bajraan/Sienkiewicz_TOUCH/__QR/Github.Sienkiewicz_TOUCH.png

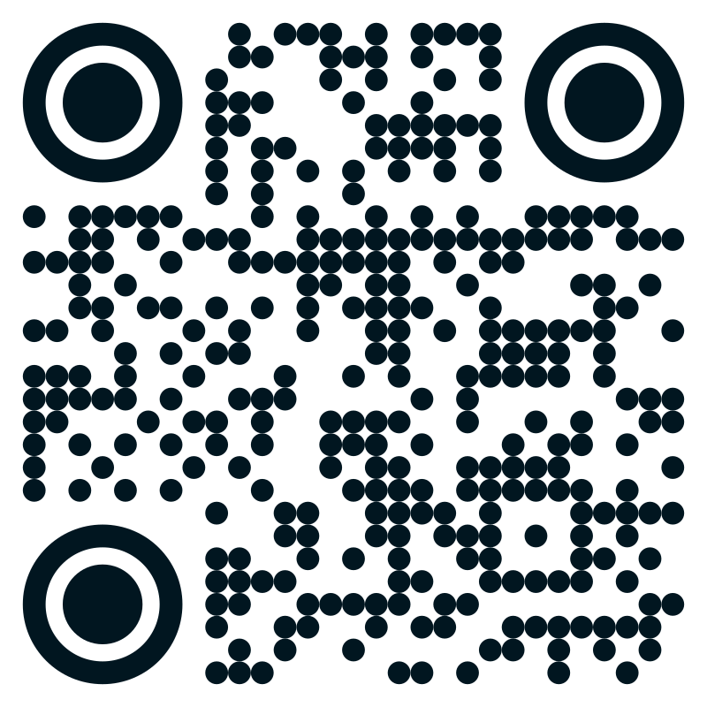
__QR/Github.Sienkiewicz_TOUCH.png
