bajraan/Sienkiewicz_TOUCH/HTML/images/cat_pdf_drill_map_Sienkiewicz_TOUCH-PTH_drill_map.png

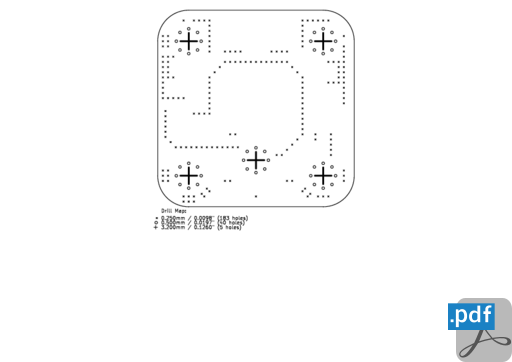
HTML/images/cat_pdf_drill_map_Sienkiewicz_TOUCH-PTH_drill_map.png
