bajraan/Sienkiewicz_TOUCH/HTML/images/cat_png_3d_viewer_angled_bottom_Sienkiewicz_TOUCH-angled_bottom.png

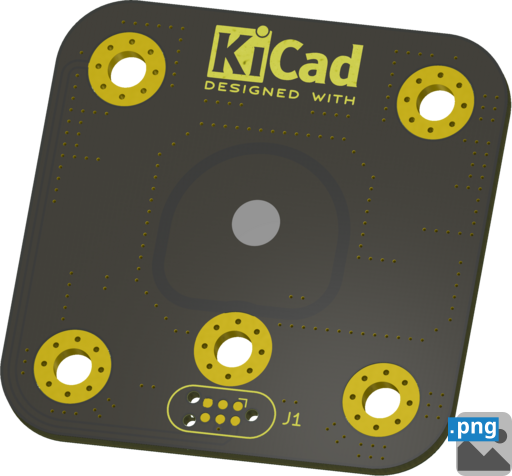
HTML/images/cat_png_3d_viewer_angled_bottom_Sienkiewicz_TOUCH-angled_bottom.png
