bajraan/Sienkiewicz_TOUCH/HTML/images/cat_png_3d_viewer_bottom_Sienkiewicz_TOUCH-bottom.png

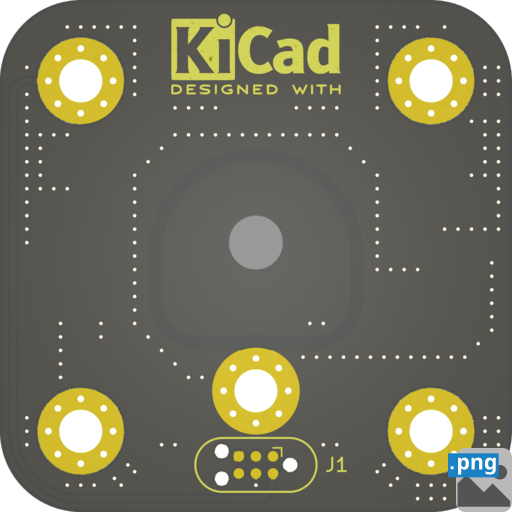
HTML/images/cat_png_3d_viewer_bottom_Sienkiewicz_TOUCH-bottom.png
