bajraan/Sienkiewicz_TOUCH/HTML/images/cat_png_3d_viewer_top_Sienkiewicz_TOUCH-top.png

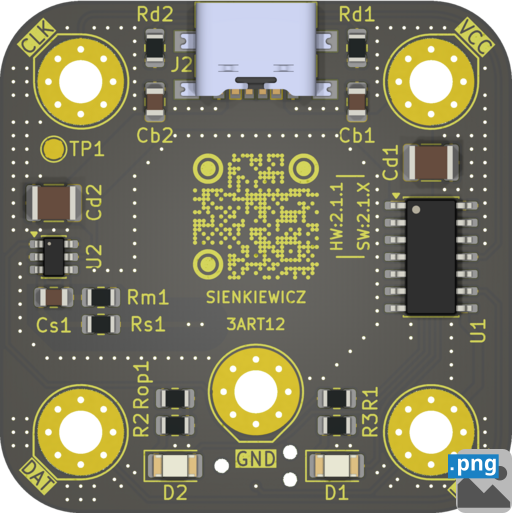
HTML/images/cat_png_3d_viewer_top_Sienkiewicz_TOUCH-top.png
