bajraan/Sienkiewicz_TOUCH/Manufacturing/Fabrication/Sienkiewicz_TOUCH-fabrication.pdf

# Top Fabrication (Scale 1:1)

# 3ART12 TOUCH Fabrication Document

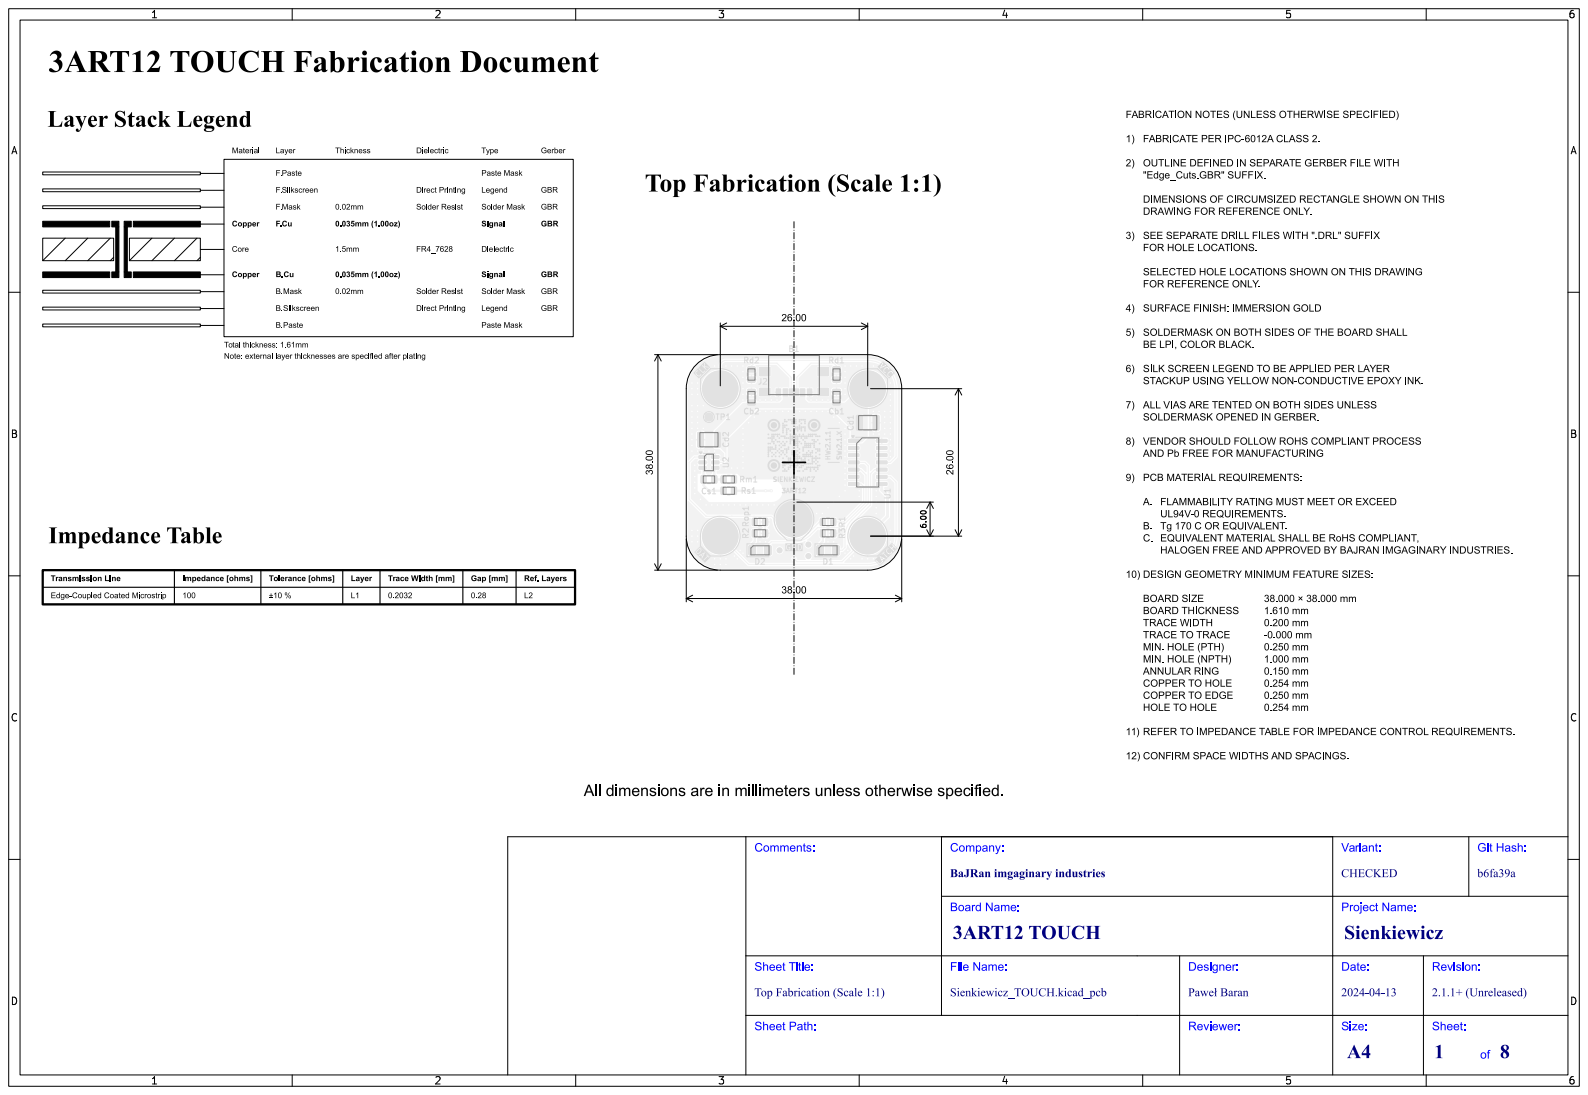
[picture p15: page 1]

# Bottom Fabrication (Scale 1:1)

# 3ART12 TOUCH Fabrication Document

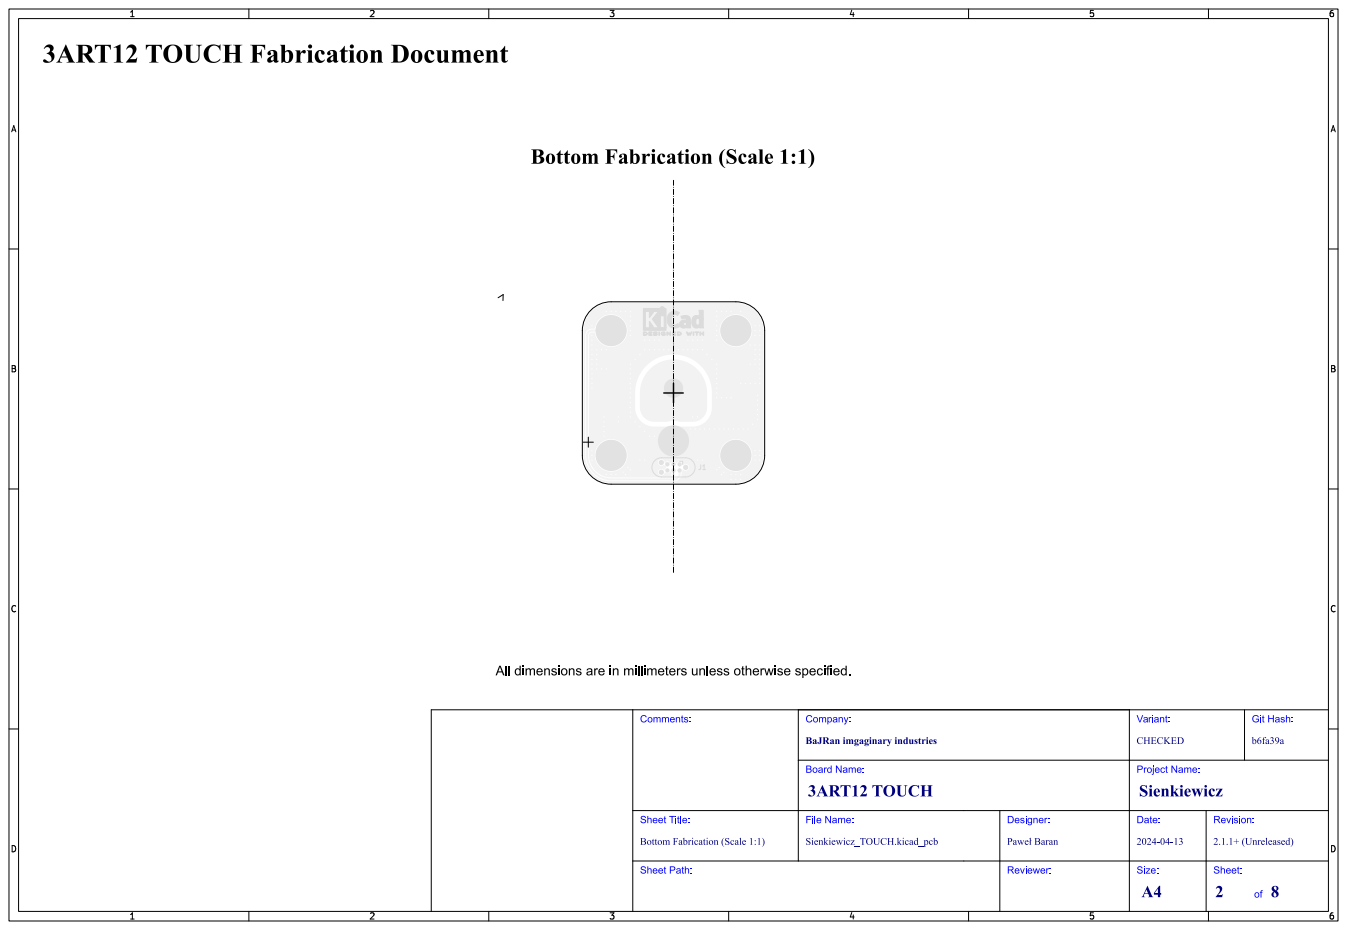
[picture p16: page 2]
Git; Hash:; Comments:; Sheet Path:; Sheet Title:; File Name:; 3ART12 TOUCH; Sienkiewicz; Company:; CHECKED; Variant:; Board Name:; Sienkiewicz_TOUCH.kicad_pcb; Paweł Baran; Designer:; Reviewer:; Project Name:; Date:; 2.1.1+ (Unreleased); Revision:; Size:; Sheet:

BaJRan imgaginary industries

Bottom Fabrication (Scale 1:1)

# Drill Drawing L1 - L2 (Scale 1:1)

# 3ART12 TOUCH Fabrication Document

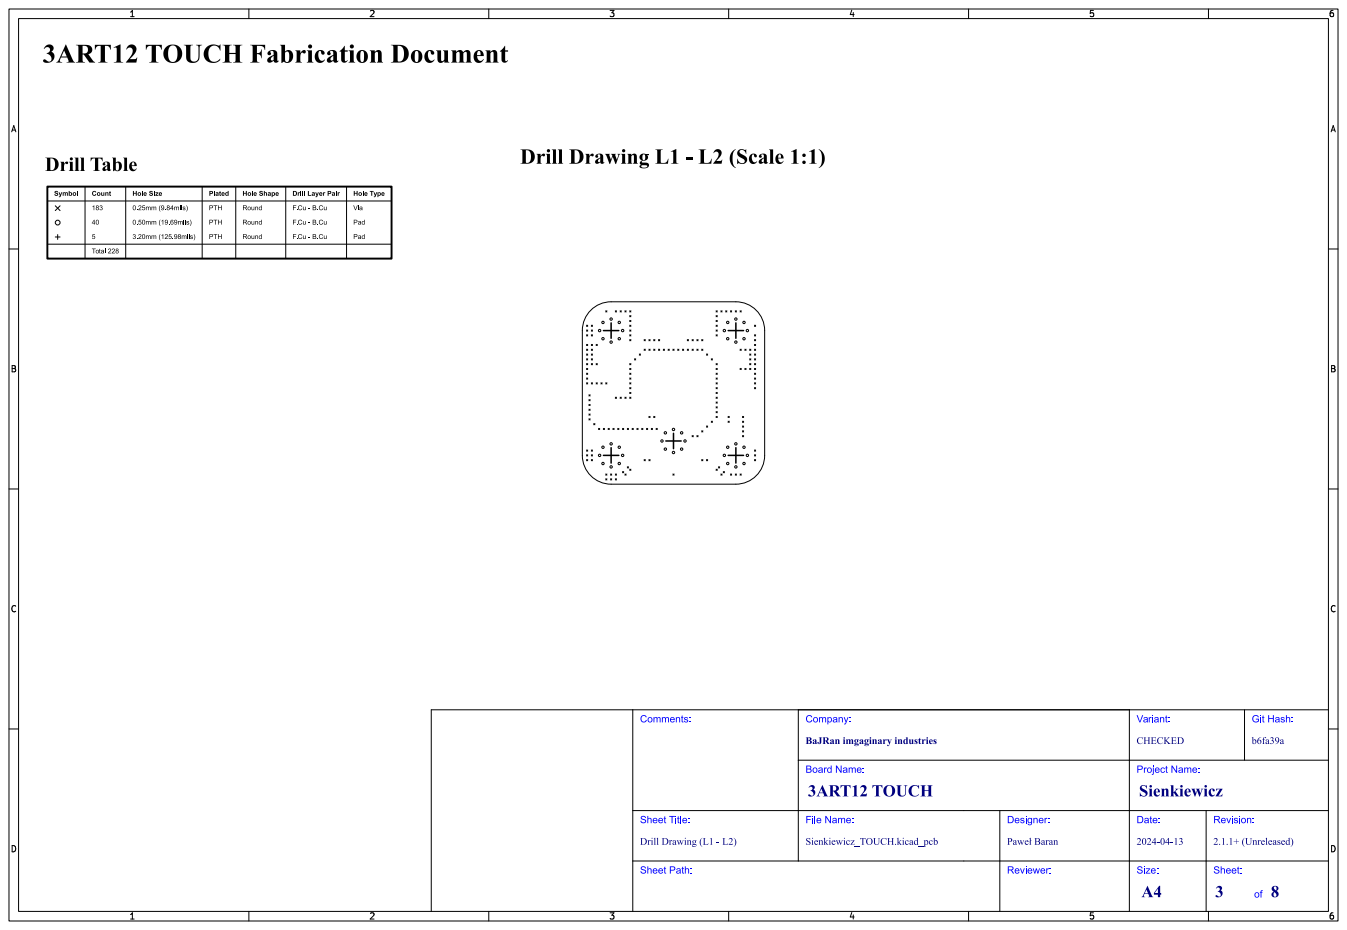
[picture p17: page 3]
Git; Hash:; Comments:; Drill Drawing (L1 - L2); Sheet Path:; Sheet Title:; File Name:; 3ART12 TOUCH; Sienkiewicz; Company:; CHECKED; Variant:; Board Name:; Sienkiewicz_TOUCH.kicad_pcb; Paweł Baran; Designer:; Reviewer:; Project Name:; Date:; 2.1.1+ (Unreleased); Revision:; Size:; Sheet:

BaJRan imgaginary industries

# Drill Drawing L1 - L2 (Scale 1:1)

# 3ART12 TOUCH Fabrication Document

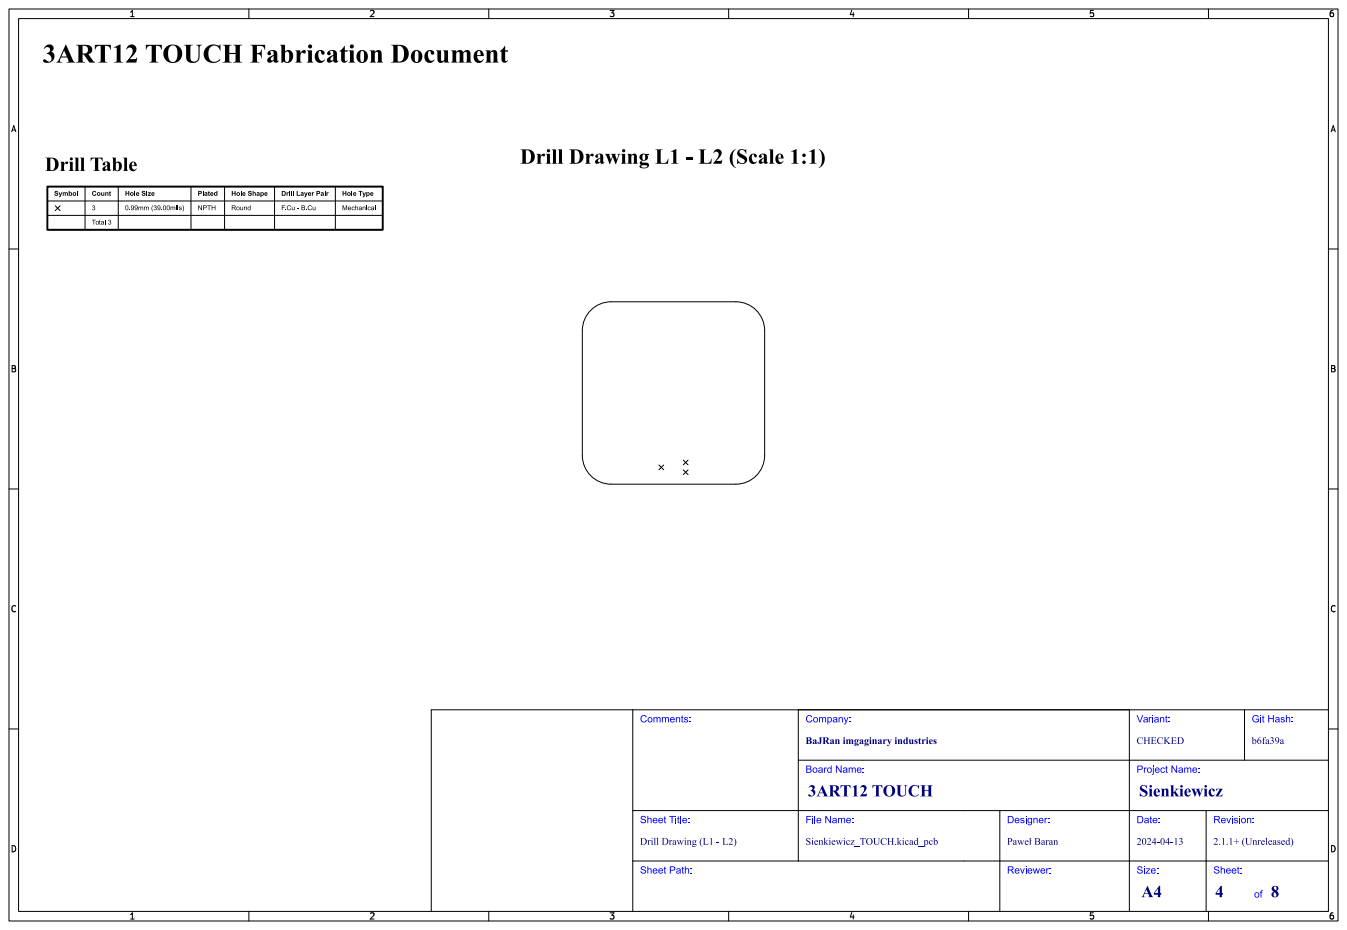
[picture p18: page 4]
Git; Hash:; Comments:; Drill Drawing (L1 - L2); Sheet Path:; Sheet Title:; File Name:; 3ART12 TOUCH; Sienkiewicz; Company:; CHECKED; Variant:; Board Name:; Sienkiewicz_TOUCH.kicad_pcb; Paweł Baran; Designer:; Reviewer:; Project Name:; Date:; 2.1.1+ (Unreleased); Revision:; Size:; Sheet:

BaJRan imgaginary industries

# Top Test Points (Scale 1:1)

# 3ART12 TOUCH Fabrication Document

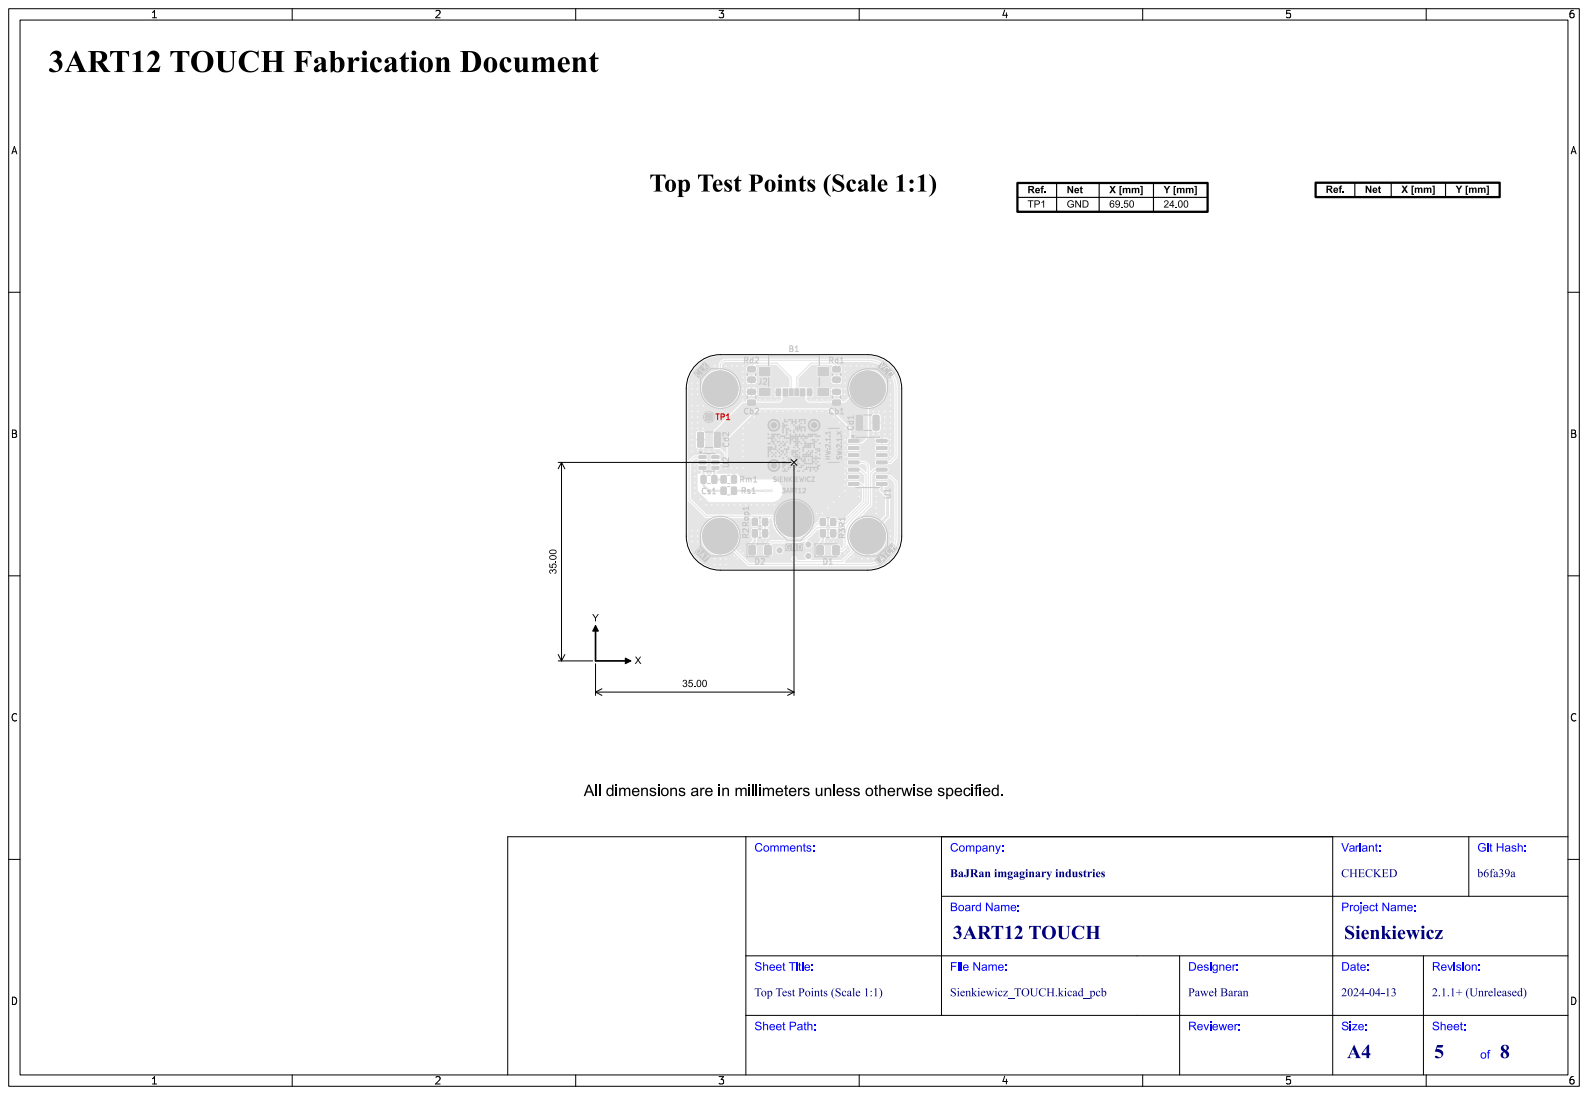
[picture p19: page 5]

Top Test Points (Scale 1:1)

# Bottom Test Points (Scale 1:1)

# 3ART12 TOUCH Fabrication Document

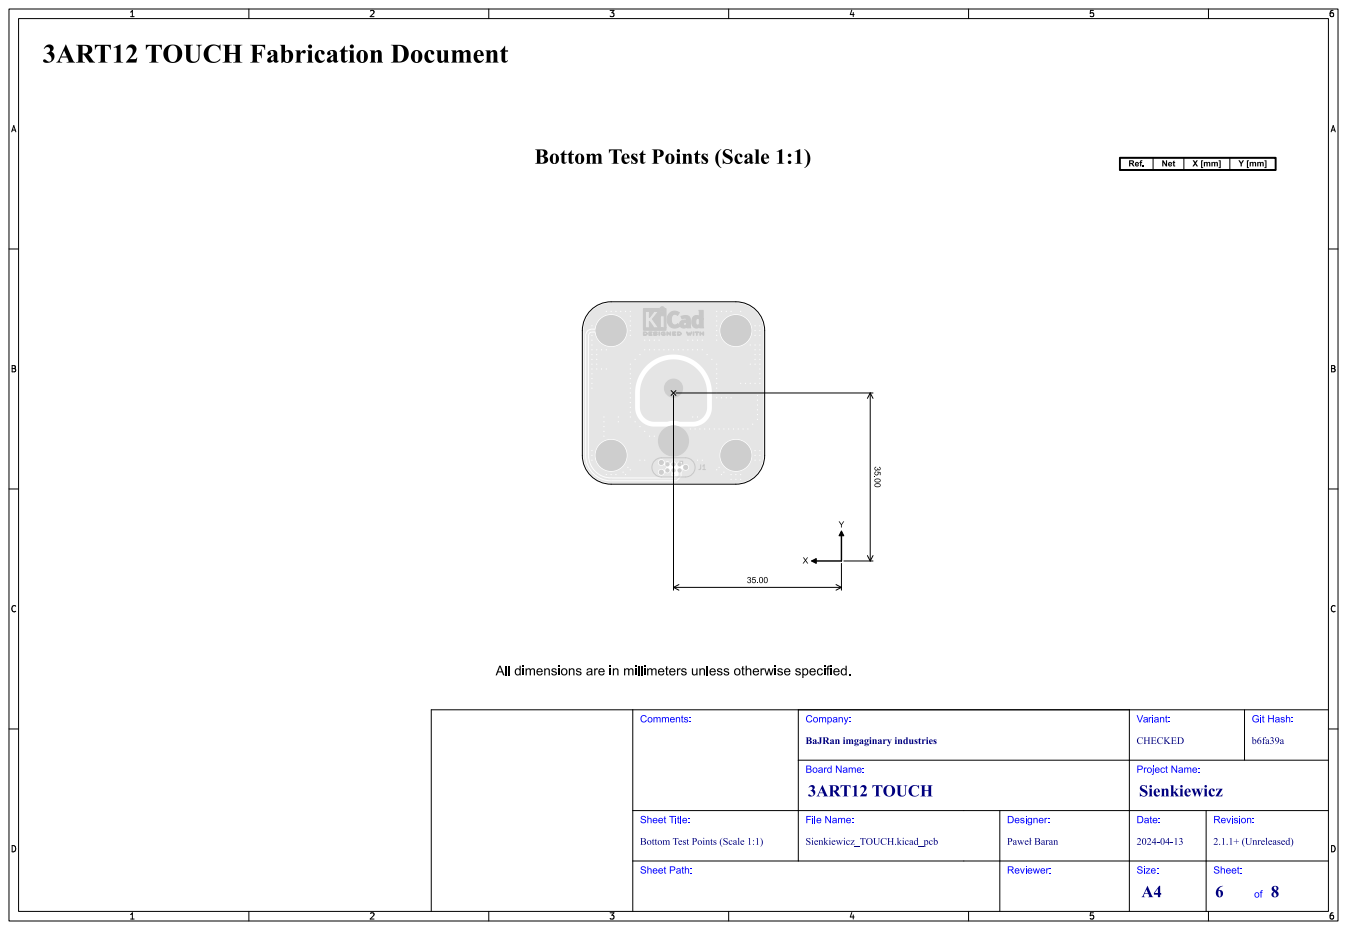
[picture p20: page 6]
Git; Hash:; Comments:; Sheet Path:; Sheet Title:; File Name:; 3ART12 TOUCH; Sienkiewicz; Company:; CHECKED; Variant:; Board Name:; Sienkiewicz_TOUCH.kicad_pcb; Paweł Baran; Designer:; Reviewer:; Project Name:; Date:; 2.1.1+ (Unreleased); Revision:; Size:; Sheet:

BaJRan imgaginary industries

Bottom Test Points (Scale 1:1)

# F.Cu (Scale 1:1)

# 3ART12 TOUCH Fabrication Document

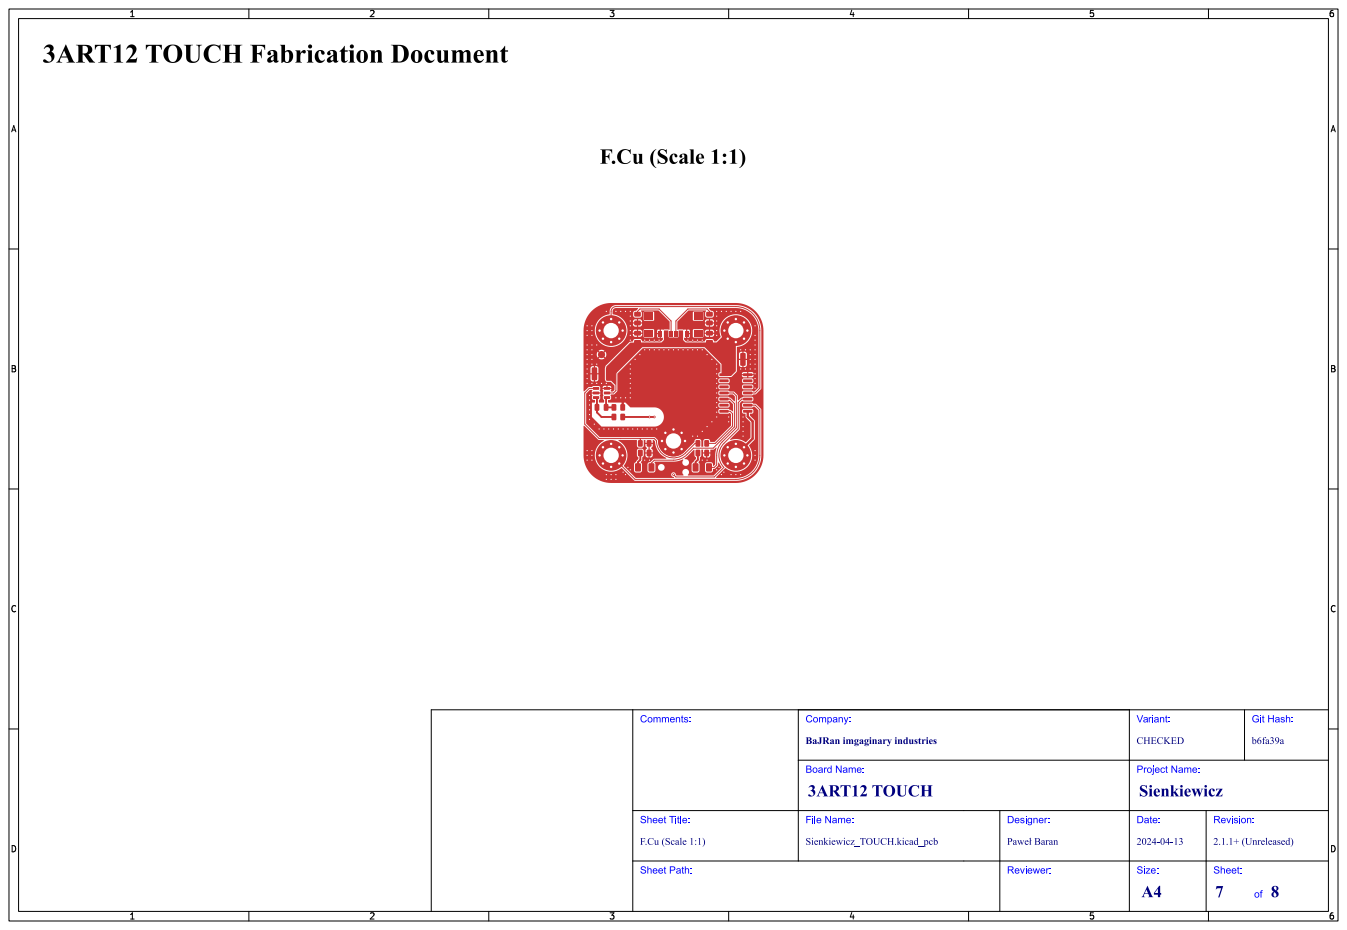
[picture p21: page 7]
Git; Hash:; Comments:; F.Cu (Scale 1:1); Sheet Path:; Sheet Title:; File Name:; 3ART12 TOUCH; Sienkiewicz; Company:; CHECKED; Variant:; Board Name:; Sienkiewicz_TOUCH.kicad_pcb; Paweł Baran; Designer:; Reviewer:; Project Name:; Date:; 2.1.1+ (Unreleased); Revision:; Size:; Sheet:

BaJRan imgaginary industries

# B.Cu (Scale 1:1)

# 3ART12 TOUCH Fabrication Document

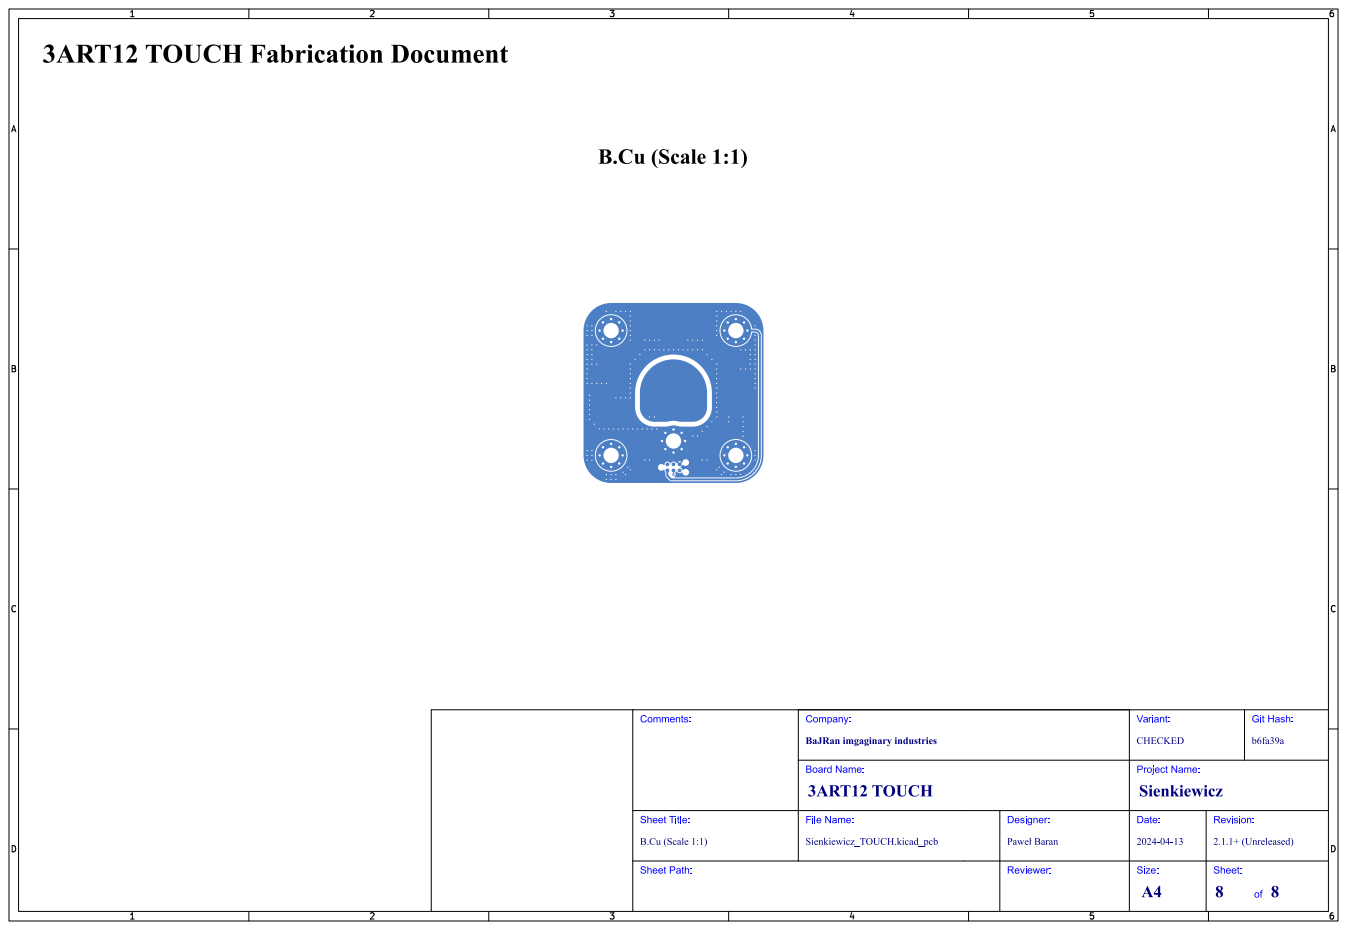
[picture p22: page 8]
Git; Hash:; Comments:; B.Cu (Scale 1:1); Sheet Path:; Sheet Title:; File Name:; 3ART12 TOUCH; Sienkiewicz; Company:; CHECKED; Variant:; Board Name:; Sienkiewicz_TOUCH.kicad_pcb; Paweł Baran; Designer:; Reviewer:; Project Name:; Date:; 2.1.1+ (Unreleased); Revision:; Size:; Sheet:

BaJRan imgaginary industries
