bajraan/Sienkiewicz_TOUCH/Manufacturing/Assembly/Sienkiewicz_TOUCH-assembly-3.pdf

# Bottom Assembly (Scale 1:1)

# 3ART12 TOUCH Assembly Document

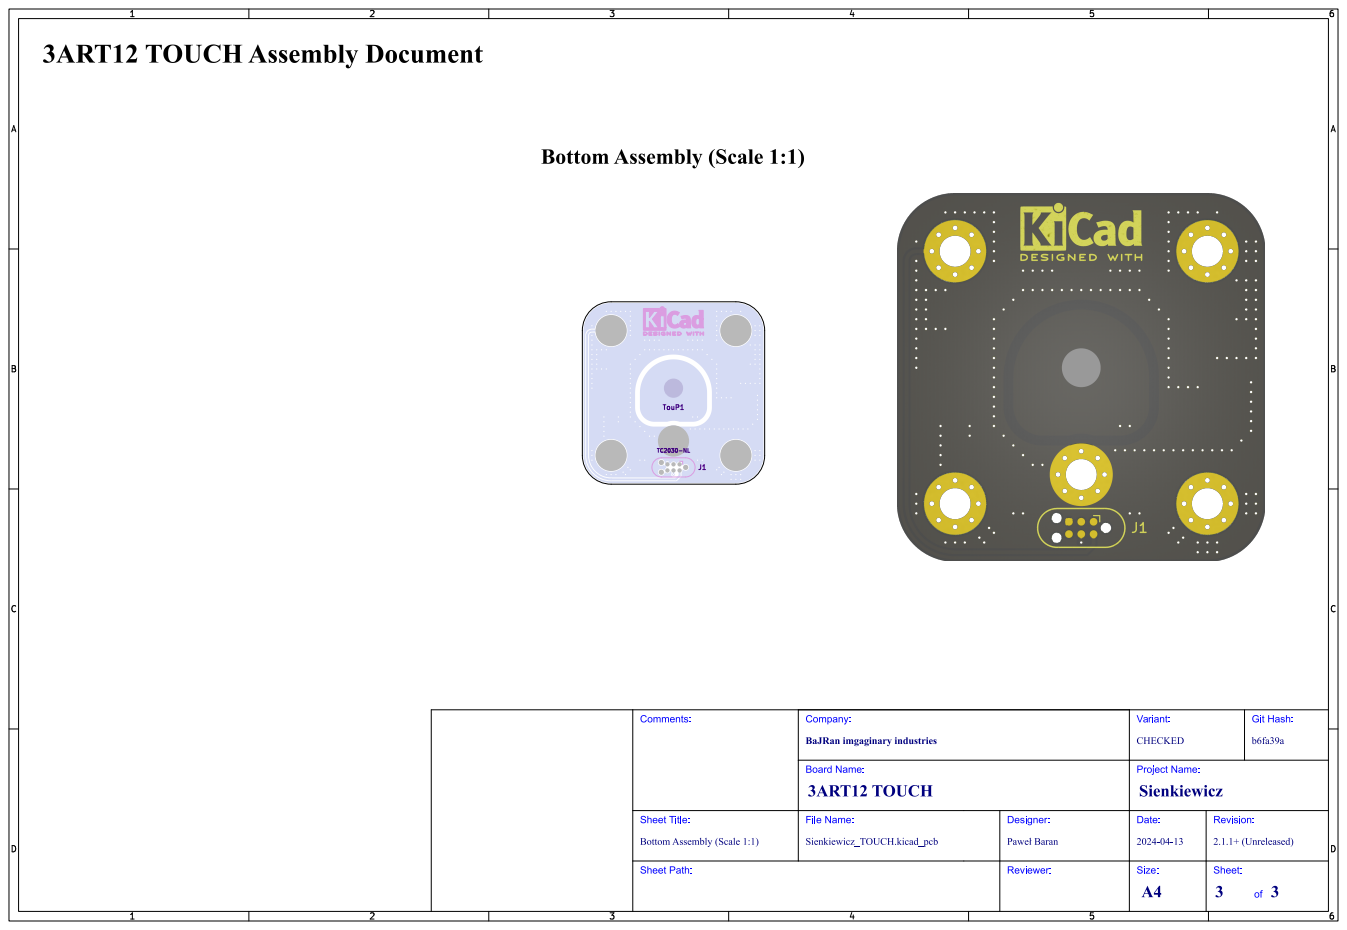
[picture p35: page 1]
Git; Hash:; Comments:; Sheet Path:; Sheet Title:; File Name:; 3ART12 TOUCH; Sienkiewicz; Company:; CHECKED; Variant:; Board Name:; Sienkiewicz_TOUCH.kicad_pcb; Paweł Baran; Designer:; Reviewer:; Project Name:; Date:; 2.1.1+ (Unreleased); Revision:; Size:; Sheet: 3; TouP1

BaJRan imgaginary industries

Bottom Assembly (Scale 1:1)
