bajraan/Sienkiewicz_TOUCH/Manufacturing/Assembly/Sienkiewicz_TOUCH-assembly.pdf

# 3ART12 TOUCH Assembly Document

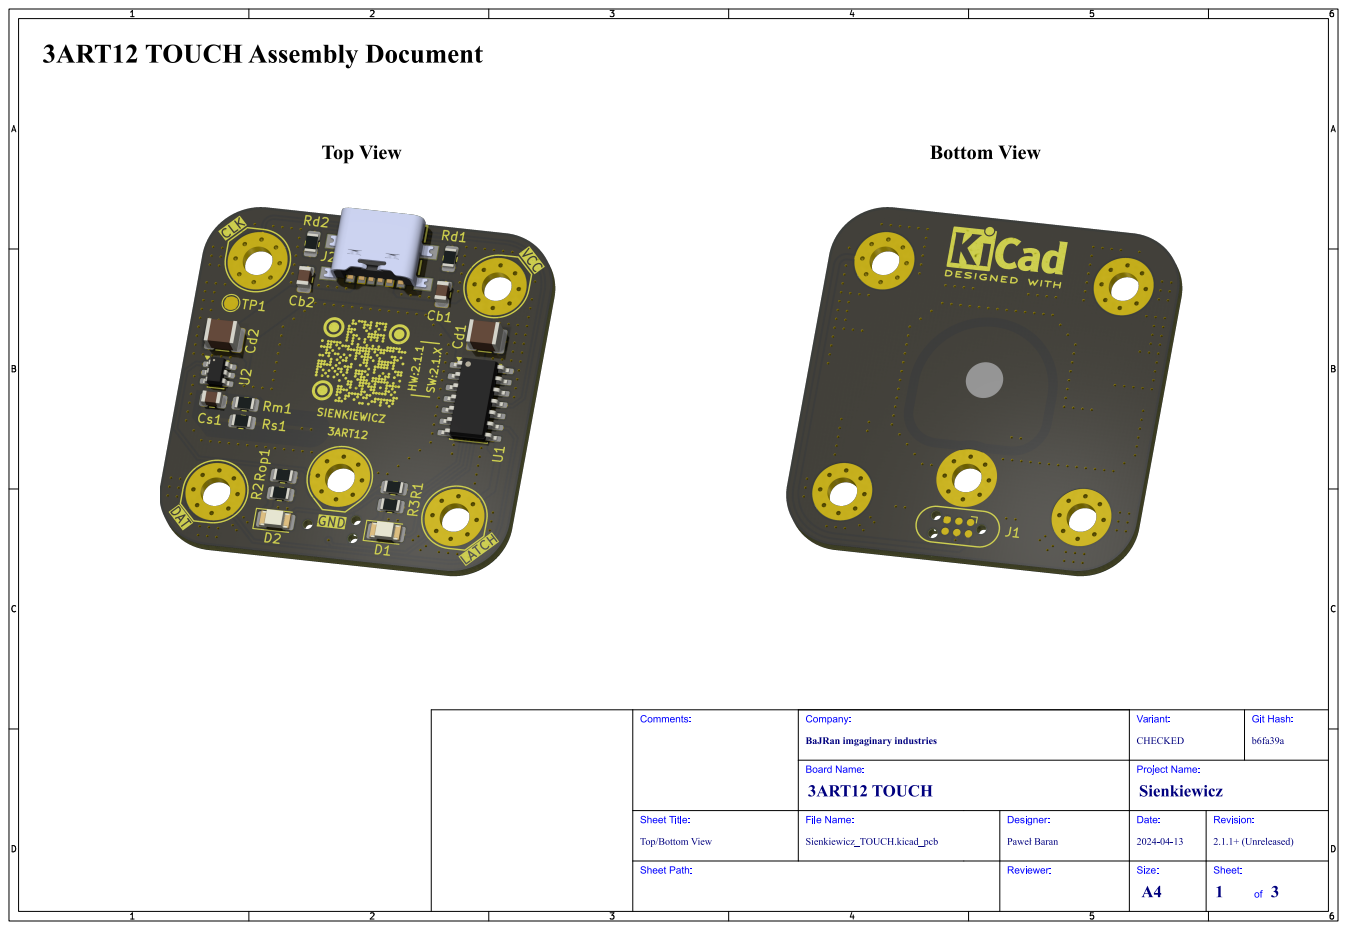
[picture p36: page 1]
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

BaJRan imgaginary industries

Top/Bottom View

# Top Assembly (Scale 1:1)

# 3ART12 TOUCH Assembly Document


# Bottom Assembly (Scale 1:1)

# 3ART12 TOUCH Assembly Document

Git; Hash:; Comments:; Sheet Path:; Sheet Title:; File Name:; 3ART12 TOUCH; Sienkiewicz; Company:; CHECKED; Variant:; Board Name:; Sienkiewicz_TOUCH.kicad_pcb; Paweł Baran; Designer:; Reviewer:; Project Name:; Date:; 2.1.1+ (Unreleased); Revision:; Size:; Sheet:; TouP1

BaJRan imgaginary industries

Bottom Assembly (Scale 1:1)
