bajraan/Sienkiewicz_TOUCH/Manufacturing/Fabrication/Sienkiewicz_TOUCH-fabrication-2.pdf

# Bottom Fabrication (Scale 1:1)

# 3ART12 TOUCH Fabrication Document

Git; Hash:; Comments:; Sheet Path:; Sheet Title:; File Name:; 3ART12 TOUCH; Sienkiewicz; Company:; CHECKED; Variant:; Board Name:; Sienkiewicz_TOUCH.kicad_pcb; Paweł Baran; Designer:; Reviewer:; Project Name:; Date:; 2.1.1+ (Unreleased); Revision:; Size:; Sheet: 2

BaJRan imgaginary industries

Bottom Fabrication (Scale 1:1)
