bajraan/Sienkiewicz_TOUCH/Manufacturing/Fabrication/Sienkiewicz_TOUCH-fabrication-1.pdf

# Top Fabrication (Scale 1:1)

# 3ART12 TOUCH Fabrication Document
