bajraan/Sienkiewicz_TOUCH/Manufacturing/Fabrication/Sienkiewicz_TOUCH-fabrication-5.pdf

# Top Test Points (Scale 1:1)

# 3ART12 TOUCH Fabrication Document


Top Test Points (Scale 1:1)
