bajraan/Sienkiewicz_TOUCH/Manufacturing/Fabrication/Gerbers/Sienkiewicz_TOUCH-NPTH_drill_map.pdf

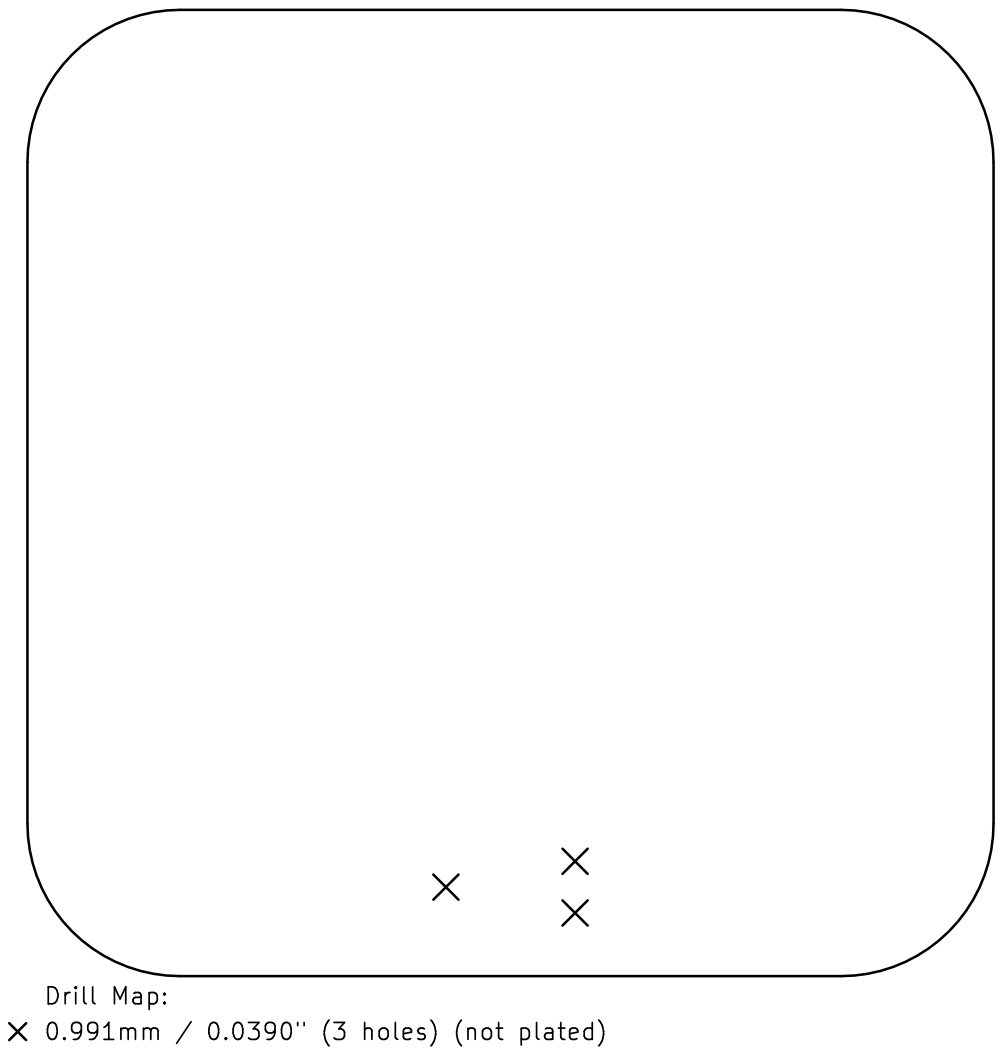
[picture p37: page 1]
