bajraan/Sienkiewicz_TOUCH/Manufacturing/Fabrication/Gerbers/Sienkiewicz_TOUCH-PTH_drill_map.pdf

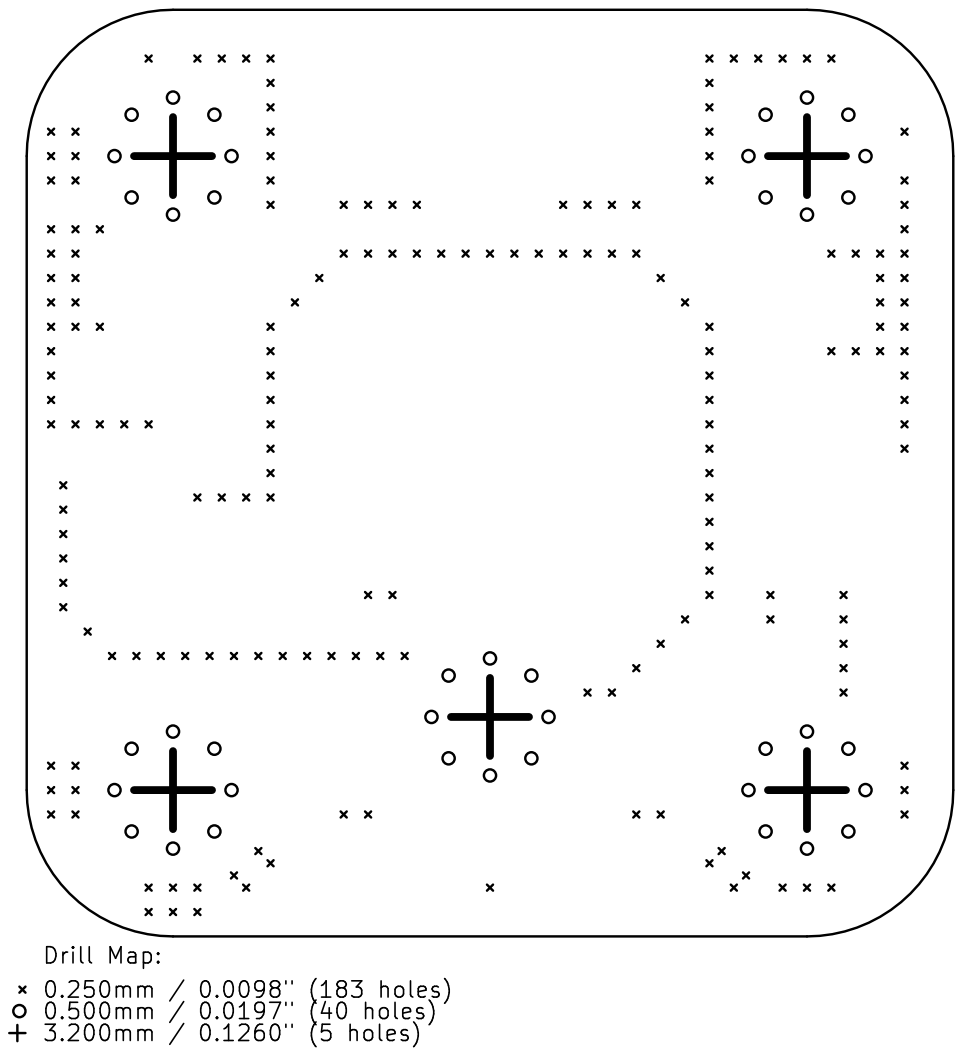
[picture p38: page 1]
